MustafaBiyikli/SMAQ/Resources/api.gif

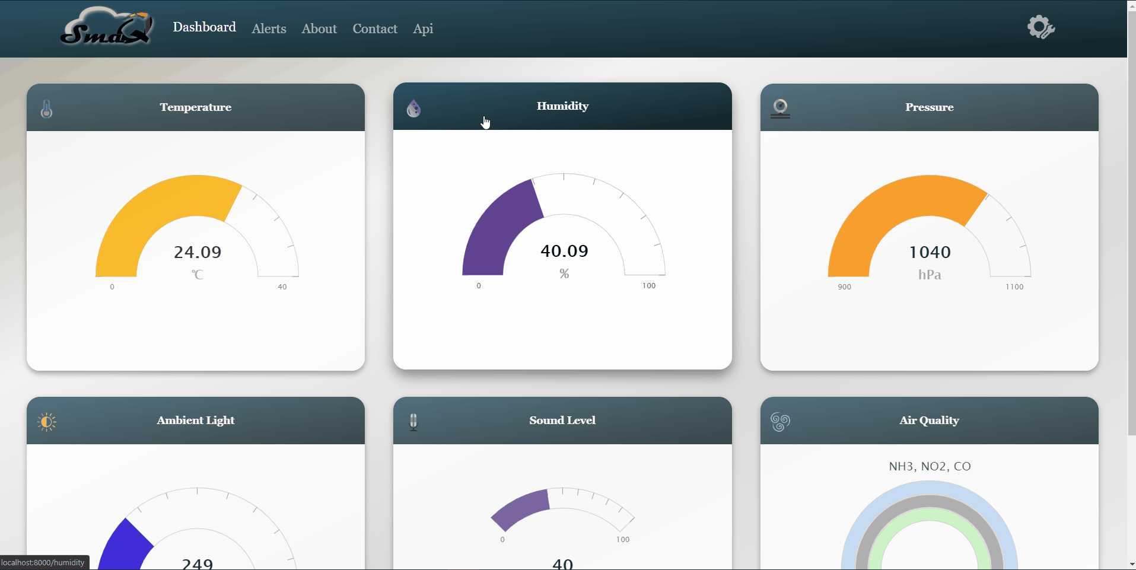
Resources/api.gif
