MustafaBiyikli/SMAQ/Resources/BoxMockupbackside.png

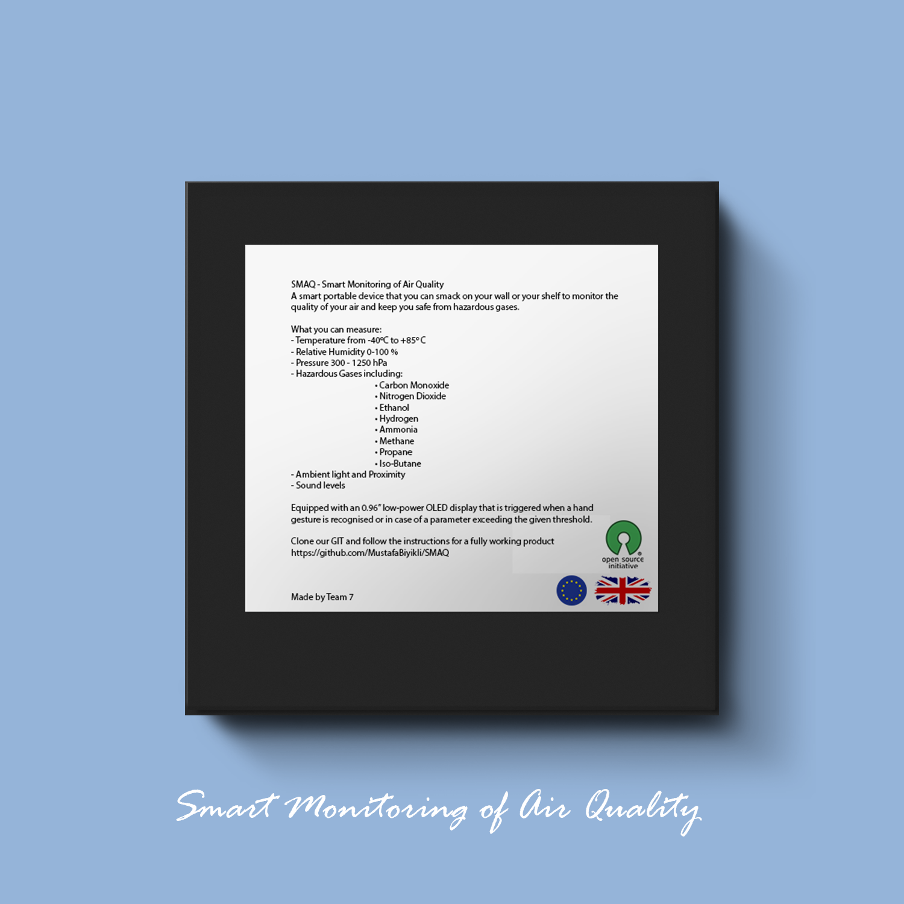
Resources/BoxMockupbackside.png
