MustafaBiyikli/SMAQ/Resources/BoxMockupSide.png

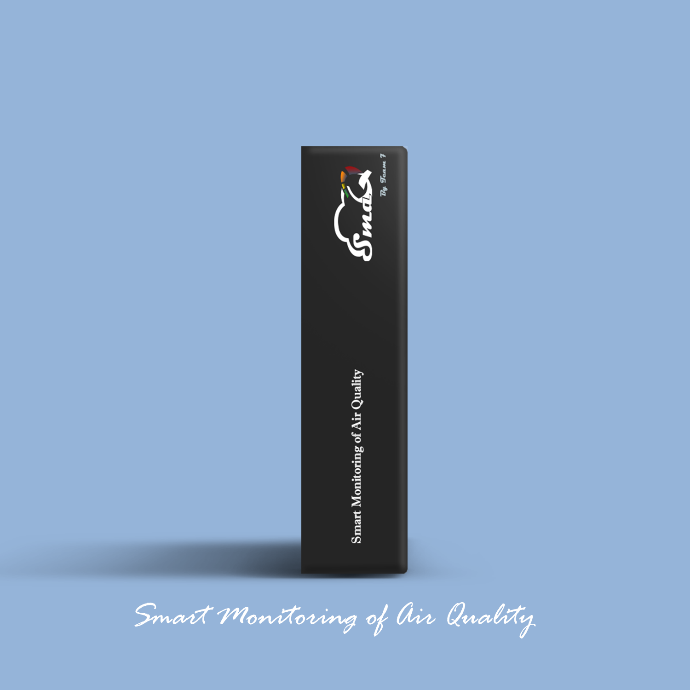
Resources/BoxMockupSide.png
