MustafaBiyikli/SMAQ/Resources/WithBlueBackground.png

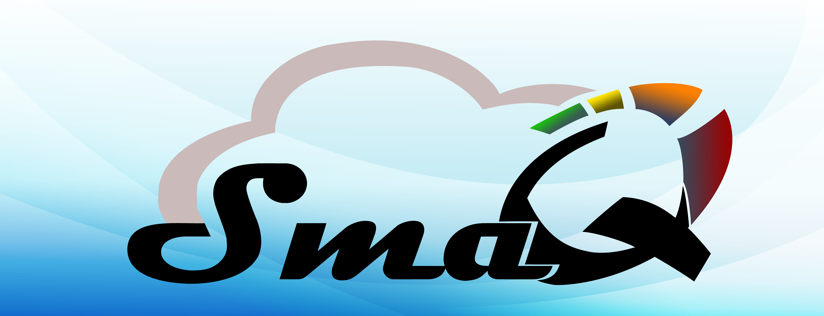
Resources/WithBlueBackground.png
