MustafaBiyikli/SMAQ/Software/Website/img/bgcoral2.jpg

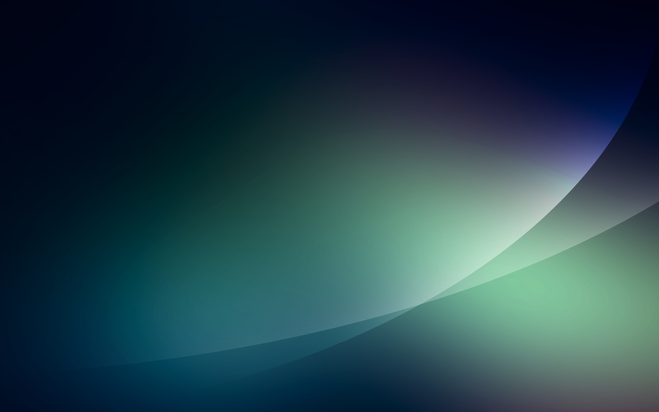
Software/Website/img/bgcoral2.jpg
