MustafaBiyikli/SMAQ/Software/Website/img/colors.jpg

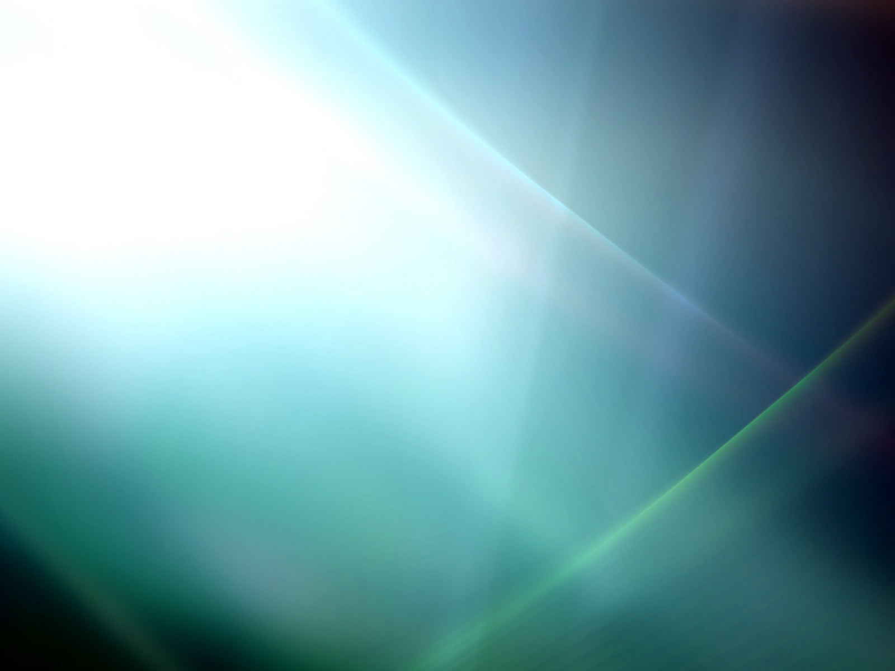
Software/Website/img/colors.jpg
