MustafaBiyikli/SMAQ/Software/Website/img/error.png

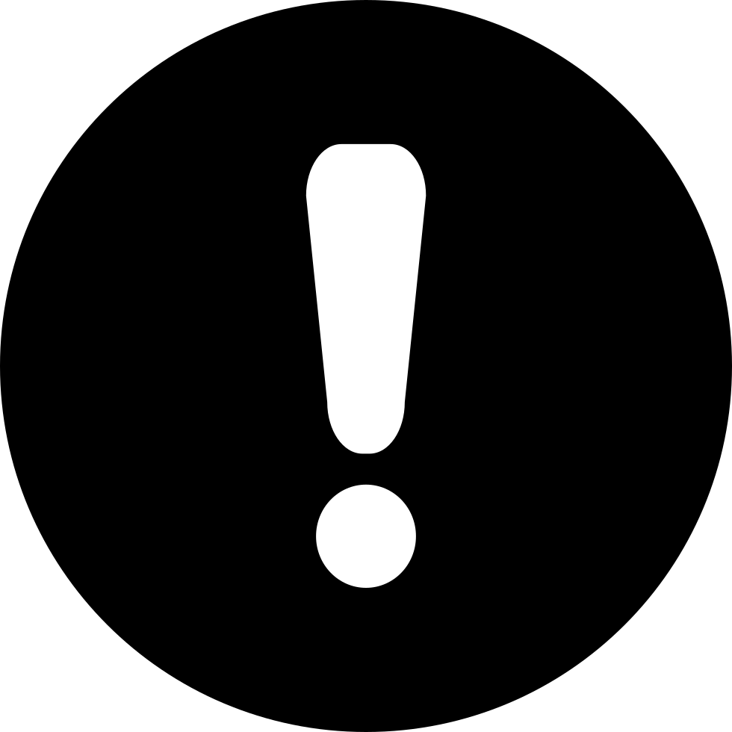
Software/Website/img/error.png
