MustafaBiyikli/SMAQ/Software/Website/img/next.png

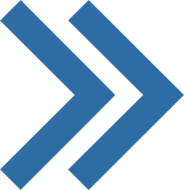
Software/Website/img/next.png
