MustafaBiyikli/SMAQ/Software/Website/img/prev.png

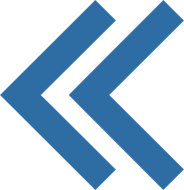
Software/Website/img/prev.png
