MustafaBiyikli/SMAQ/Software/Website/img/settings.png

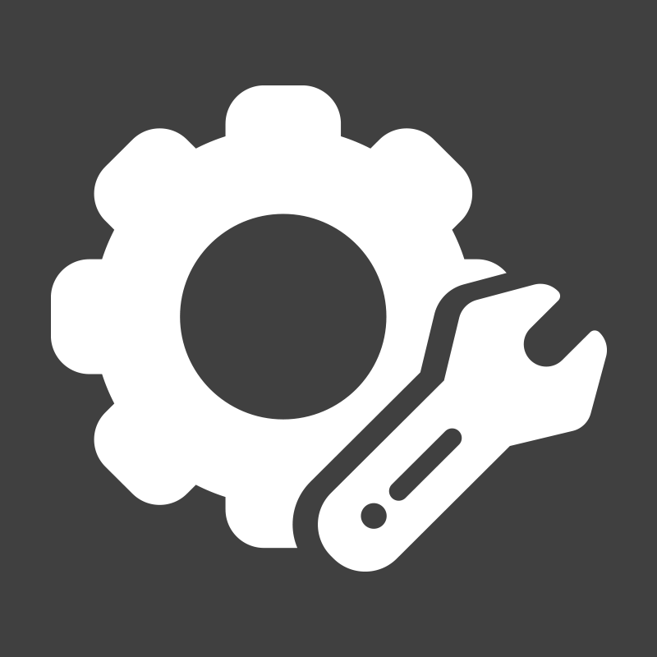
Software/Website/img/settings.png
