MustafaBiyikli/SMAQ/Software/Website/img/success.png

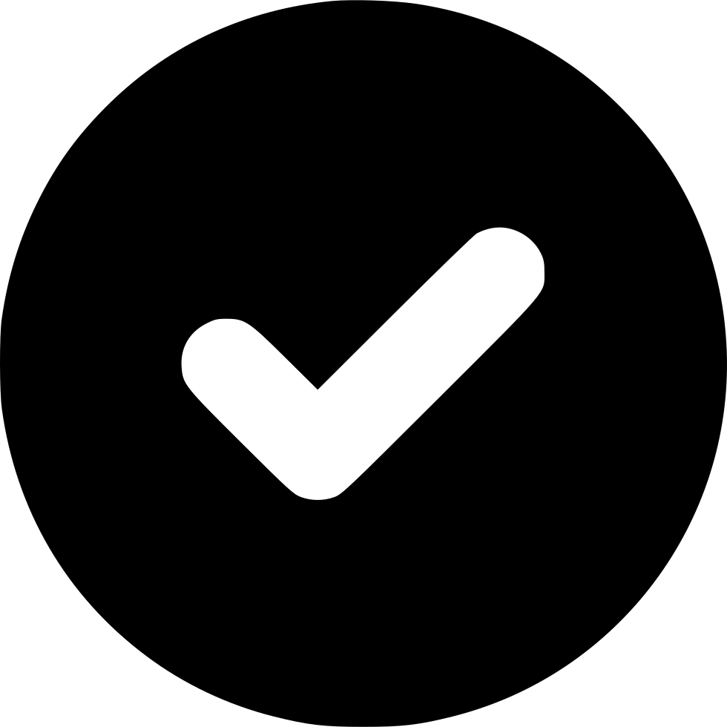
Software/Website/img/success.png
