MustafaBiyikli/SMAQ/Software/Website/img/WebBG.jpg

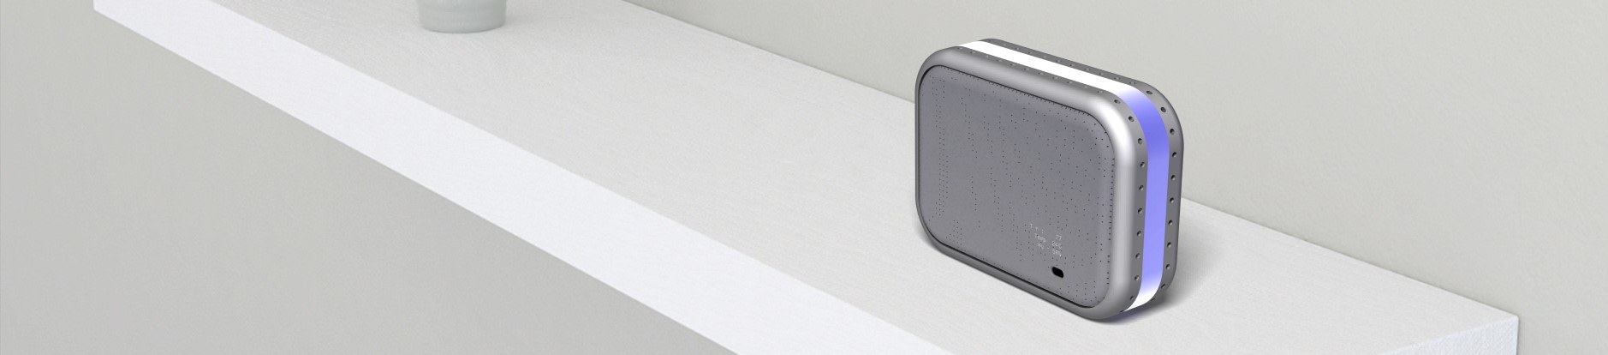
Software/Website/img/WebBG.jpg
