MustafaBiyikli/SMAQ/Hardware/PCB Manufacturing/LayerStackInfo.pdf

# Board Stack Report

Stack Up | Layer Stack
Layer | Board Layer Stack | Name | Material | Thickness | Constant

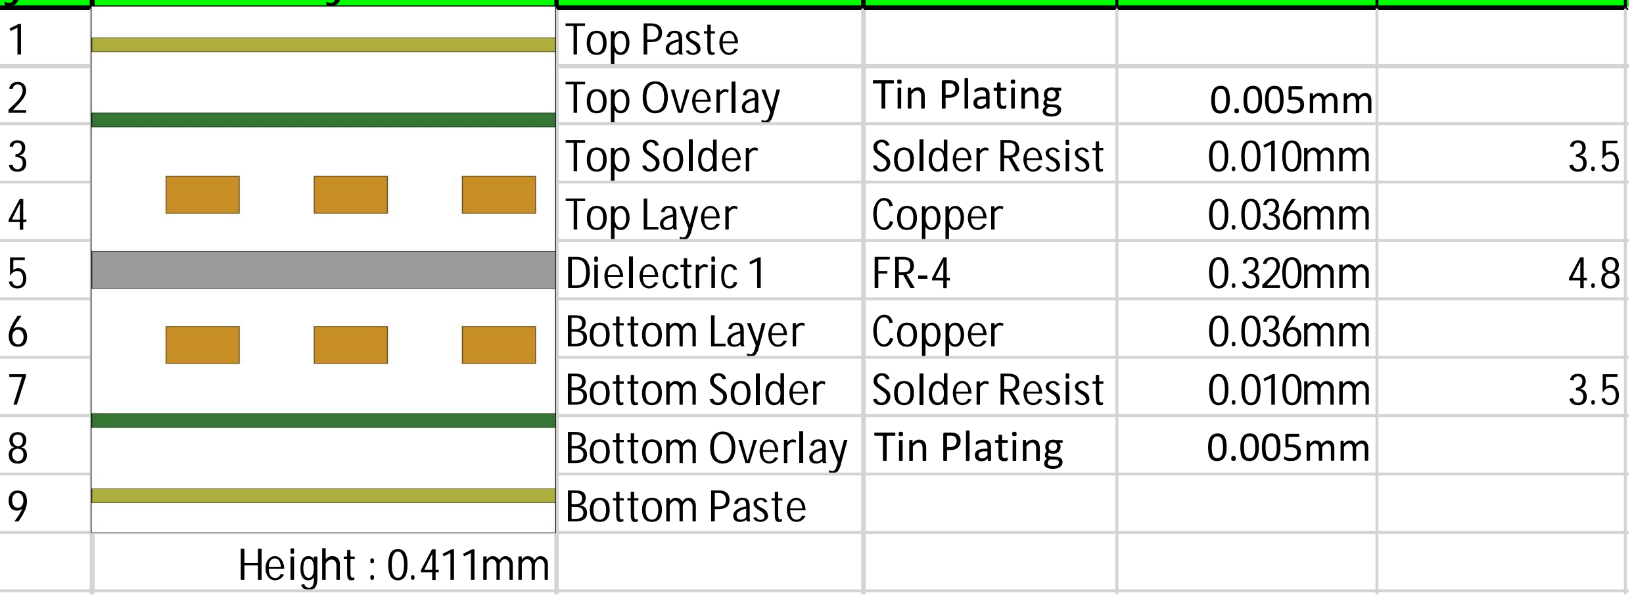
[picture p68: figure]
Top Paste; Top Overlay; Tin Plating; Top Solder; Solder Resist; Top Layer; Copper; Dielectric 1; Bottom Layer; Bottom Solder; Bottom Overlay; Bottom Paste; Height : 0.411mm
