MustafaBiyikli/SMAQ/Hardware/PCB Manufacturing/NC Drill Output/NCDrillOutput.PDF

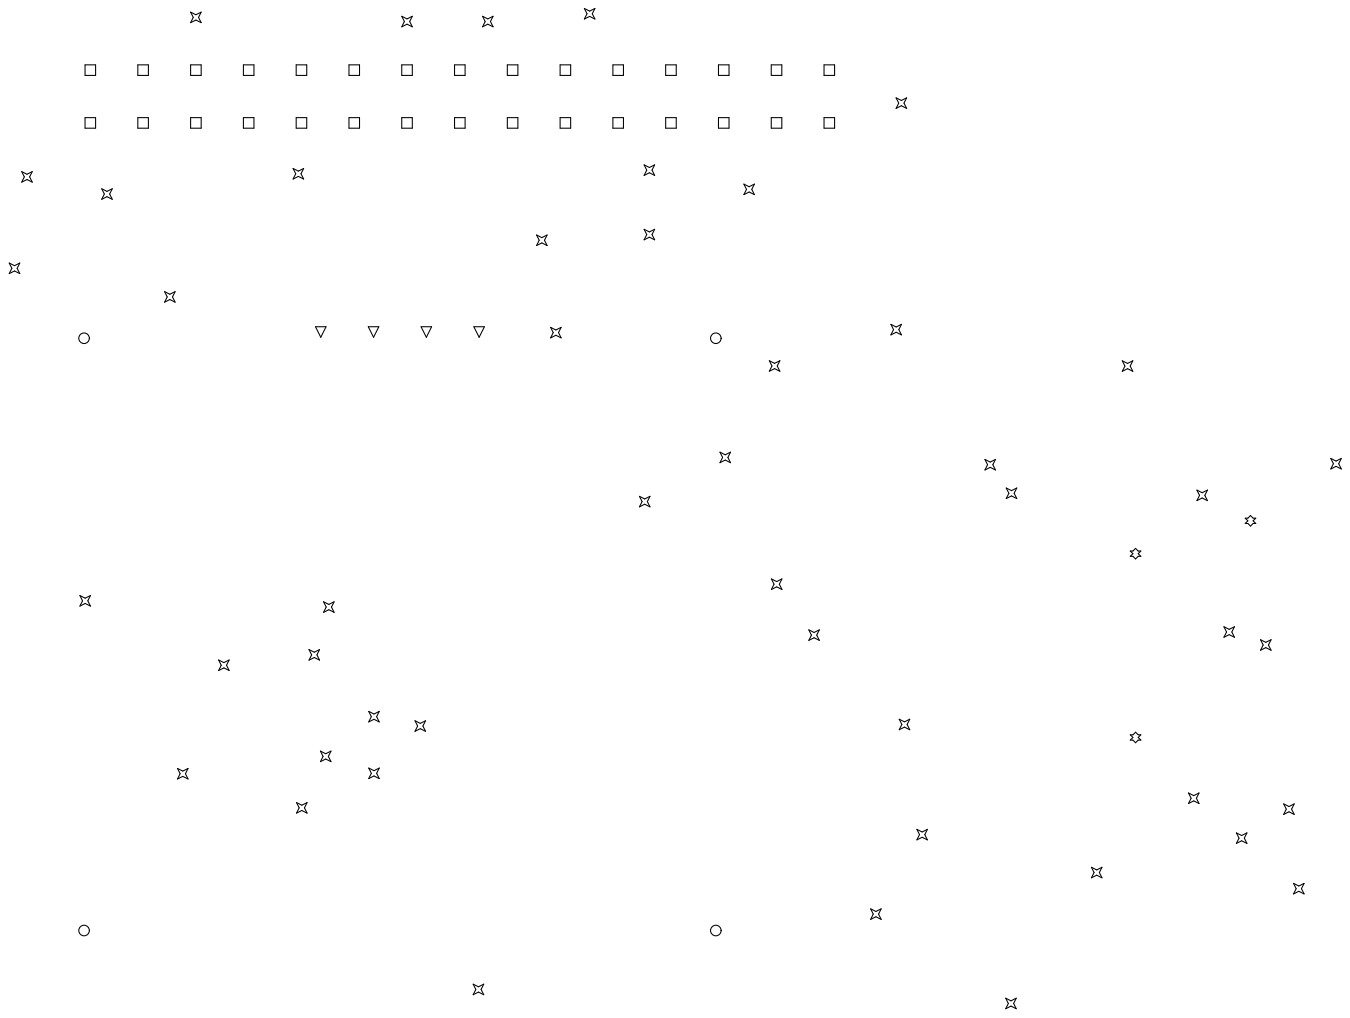
[picture p91: page 1]

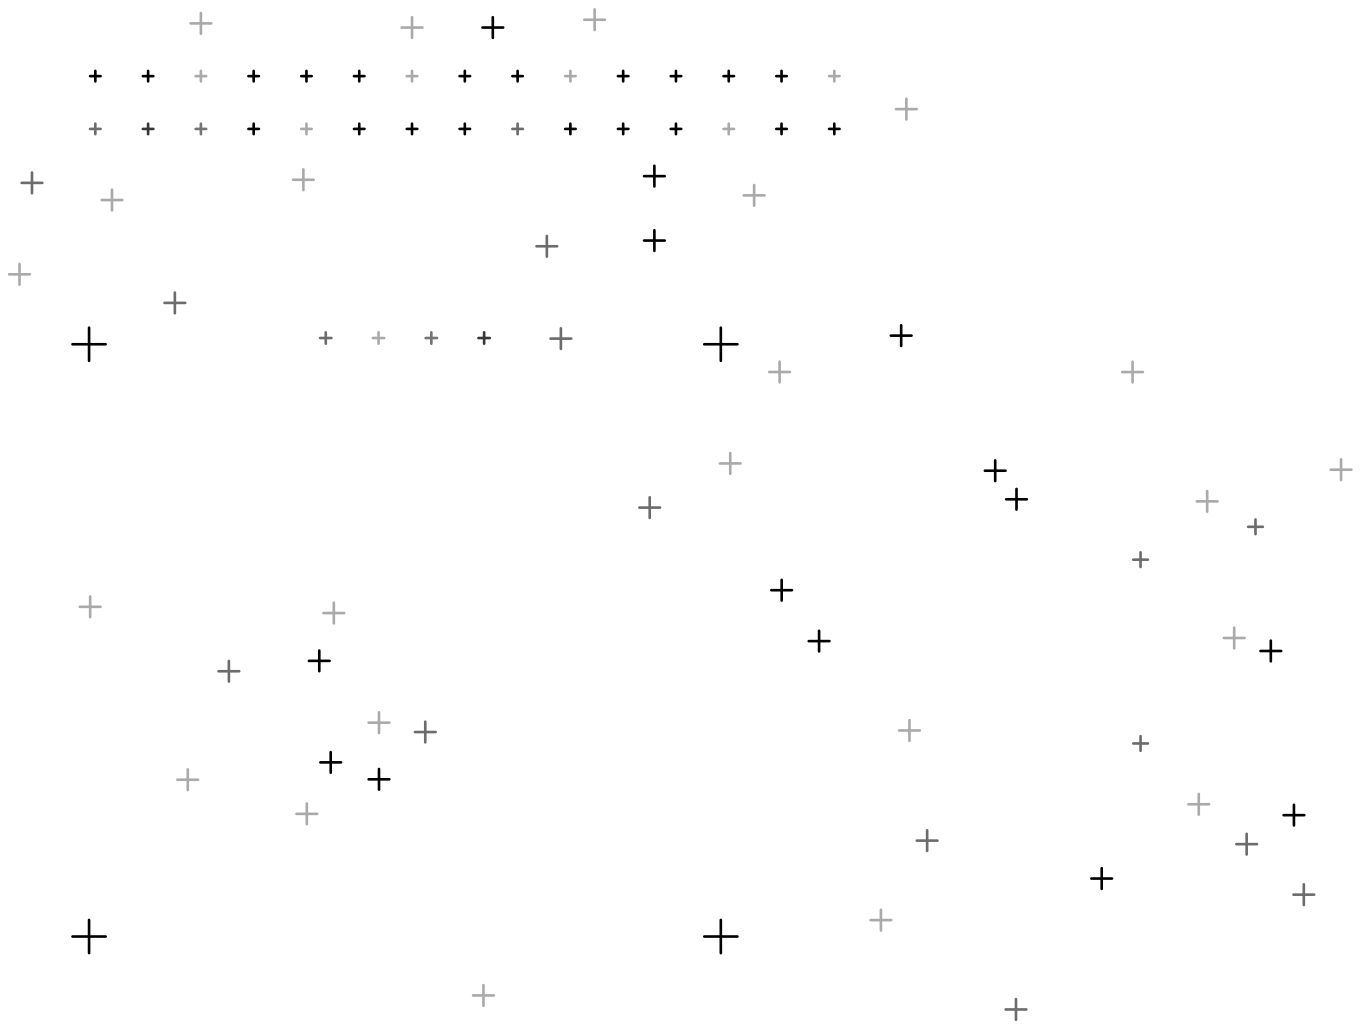
[picture p92: page 2]
