MustafaBiyikli/SMAQ/Hardware/HW_Resources/UofG-Board-etching-SMAQ.pdf

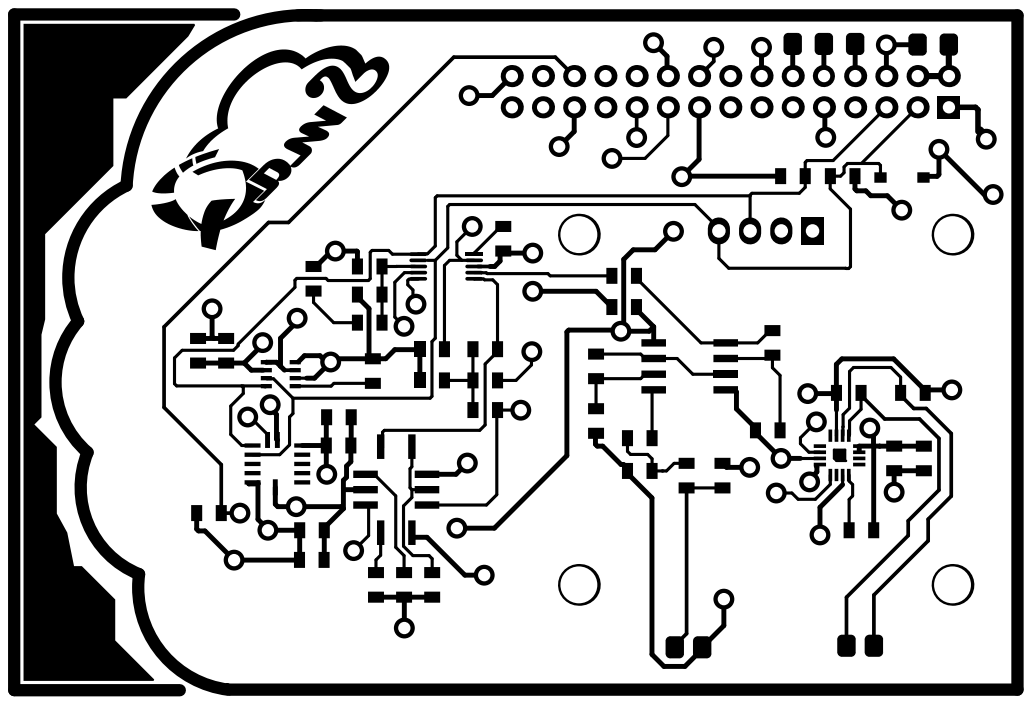
[picture p93: page 1]

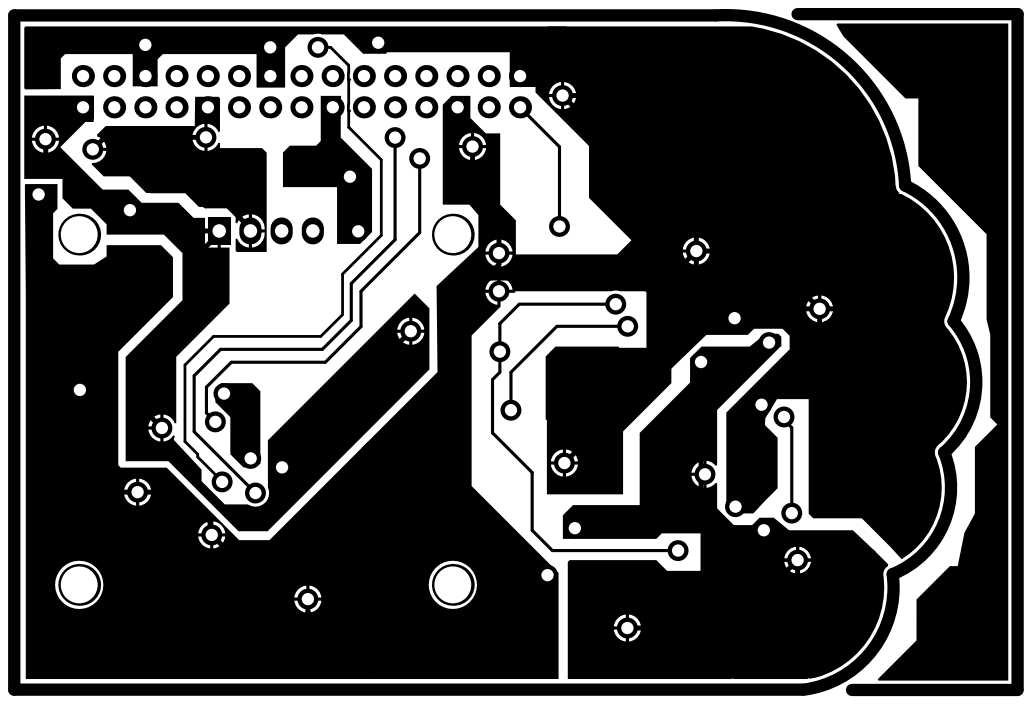
[picture p94: page 2]
