MustafaBiyikli/SMAQ/Software/Real-Time/SH1106.h

#ifndef __SH1106_H__
#define __SH1106_H__

#include <string>
#include <iostream>
using namespace std;

#define rotation 0
#define BLACK 0
#define WHITE 1
#define INVERSE 2

#define SH1106_ADDRESS 0x3C // 011110+SA0+RW - 0x3C or 0x3D

// We use the 128x64 version of SH1106
#define WIDTH 128
#define HEIGHT 64

#define control 0x80

#define SH1106_SETCONTRAST 0x81
#define SH1106_DISPLAYALLON_RESUME 0xA4
#define SH1106_DISPLAYALLON 0xA5
#define SH1106_NORMALDISPLAY 0xA6
#define SH1106_INVERTDISPLAY 0xA7
#define SH1106_DISPLAYOFF 0xAE
#define SH1106_DISPLAYON 0xAF

#define SH1106_SETDISPLAYOFFSET 0xD3
#define SH1106_SETCOMPINS 0xDA

#define SH1106_SETVCOMDETECT 0xDB

#define SH1106_SETDISPLAYCLOCKDIV 0xD5
#define SH1106_SETPRECHARGE 0xD9

#define SH1106_SETMULTIPLEX 0xA8

#define SH1106_SETLOWCOLUMN 0x00  // from 0x00 to 0x0F
#define SH1106_SETHIGHCOLUMN 0x10 // from 0x10 to 0x1F

#define SH1106_SETSTARTLINE 0x40 // from 0x40 to 0x7f

#define SH1106_COLUMNADDR 0x21 // from 0x00 to 0x83
#define SH1106_PAGEADDR 0x22

#define SH1106_COMSCANINC 0xC0
#define SH1106_COMSCANDEC 0xC8

#define SH1106_SEGREMAP 0xA1 // 0xA0 to 0xA1

#define SH1106_CHARGEPUMP 0x8D

#define SH1106_MEMORYMODE 0x20

#define SH1106_EXTERNALVCC 0x1
#define SH1106_SWITCHCAPVCC 0x2

class SH1106
{
public:
    /** Declare Functions */
    void sh1106_init(int fd_SH1106);
    void sh1106_display(int fd_SH1106);
    void sh1106_clearDisplay(int fd_SH1106);
    void sh1106_displayOFF(int fd_SH1106);
    void sh1106_drawPixel(int x, int y, unsigned int color);
    void sh1106_write(int c);
    void sh1106_drawString(string str);
    void sh1106_drawChar(int x, int y, unsigned char c, int color, int size = 1);
    string getDateTime(int date_or_time);
    void sh1106_displayData(int fd_SH1106, int t, int p, int h, int lux);

    // Used for date_or_time in getDateTime fn
    int DATE = 0;
    int TIME = 1;

    /** SMAQ logo bmp buffer */
    int buffer[WIDTH * HEIGHT / 8] =
        {
            0x00, 0x00, 0x00, 0x00, 0x00, 0x00, 0x00, 0x00, 0x00, 0x00, 0x00, 0x00, 0x00, 0x00, 0x00, 0x00,
            0x00, 0x00, 0x00, 0x00, 0x00, 0x00, 0x00, 0x00, 0x00, 0x00, 0x00, 0x00, 0x00, 0x00, 0x00, 0x00,
            0x00, 0x00, 0x00, 0x00, 0x00, 0x00, 0x00, 0x00, 0x00, 0x00, 0x00, 0x00, 0x00, 0x00, 0x00, 0x00,
            0x00, 0x00, 0x00, 0x00, 0x00, 0x00, 0x00, 0x00, 0x00, 0x00, 0x00, 0x00, 0x00, 0x00, 0x00, 0x00,
            0x00, 0x00, 0x00, 0x00, 0x00, 0x00, 0x00, 0x00, 0x00, 0x00, 0x00, 0x00, 0x00, 0x00, 0x00, 0x00,
            0x00, 0x00, 0x00, 0x00, 0x00, 0x00, 0x00, 0x00, 0x00, 0x00, 0x00, 0x00, 0x00, 0x00, 0x00, 0x00,
            0x00, 0x00, 0x00, 0x00, 0x00, 0x00, 0x00, 0x00, 0x00, 0x00, 0x00, 0x00, 0x00, 0x00, 0x00, 0x00,
            0x00, 0x00, 0x00, 0x00, 0x00, 0x00, 0x00, 0x00, 0x00, 0x00, 0x00, 0x00, 0x00, 0x00, 0x00, 0x00,

            0x00, 0x00, 0x00, 0x00, 0x00, 0x00, 0x00, 0x00, 0x00, 0x00, 0x00, 0x00, 0x00, 0x00, 0x00, 0x00,
            0x00, 0x00, 0x00, 0x00, 0x00, 0x00, 0x00, 0x00, 0x00, 0x00, 0x00, 0x00, 0x00, 0x00, 0x00, 0x00,
            0x00, 0x00, 0x80, 0xC0, 0xE0, 0xF0, 0x70, 0x78, 0x3C, 0x3C, 0x1C, 0x0C, 0x0E, 0x0E, 0x06, 0x06,
            0x06, 0x06, 0x06, 0x06, 0x07, 0x03, 0x03, 0x02, 0x02, 0x02, 0x06, 0x06, 0x06, 0x06, 0x06, 0x06,
            0x04, 0x0C, 0x0C, 0x1C, 0x18, 0x38, 0x30, 0x60, 0xE0, 0xC0, 0x80, 0x00, 0x00, 0x00, 0x00, 0x00,
            0x00, 0x00, 0x00, 0x00, 0x00, 0x00, 0x00, 0x00, 0x00, 0x00, 0x00, 0x00, 0x00, 0x00, 0x00, 0x00,
            0x00, 0x00, 0x00, 0x00, 0x00, 0x00, 0x00, 0x00, 0x00, 0x00, 0x00, 0x00, 0x00, 0x00, 0x00, 0x00,
            0x00, 0x00, 0x00, 0x00, 0x00, 0x00, 0x00, 0x00, 0x00, 0x00, 0x00, 0x00, 0x00, 0x00, 0x00, 0x00,

            0x00, 0x00, 0x00, 0x00, 0x00, 0x00, 0x00, 0x00, 0x00, 0x00, 0x00, 0x00, 0x00, 0x00, 0x00, 0x00,
            0x00, 0x00, 0x00, 0x00, 0x00, 0x00, 0x00, 0x00, 0x00, 0x00, 0x00, 0x00, 0x00, 0x00, 0x80, 0x80,
            0xFC, 0xFE, 0x0F, 0x03, 0x01, 0x00, 0x00, 0x00, 0x00, 0x00, 0x00, 0x00, 0x00, 0x00, 0x00, 0x00,
            0x00, 0x00, 0x00, 0x00, 0x00, 0x00, 0x00, 0x00, 0x00, 0x00, 0x00, 0x00, 0x00, 0x00, 0x00, 0x00,
            0x00, 0x00, 0x00, 0x00, 0x00, 0x00, 0x00, 0x00, 0x00, 0x01, 0x03, 0x07, 0x04, 0x00, 0x00, 0x00,
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
            0x03, 0x03, 0x01, 0x01, 0x01, 0x01, 0x00, 0x00, 0x00, 0x00, 0x00, 0x00, 0x00, 0x00, 0x00, 0x01,
            0x01, 0x01, 0x03, 0x01, 0x00, 0x00, 0x00, 0x00, 0x00, 0x00, 0x00, 0x00, 0x00, 0x00, 0x00, 0x00,

            0x00, 0x00, 0x00, 0x00, 0x00, 0x00, 0x00, 0x00, 0x00, 0x00, 0x00, 0x00, 0x00, 0x00, 0x00, 0x00,
            0x00, 0x00, 0x00, 0x00, 0x00, 0x00, 0x00, 0x00, 0x00, 0x00, 0x00, 0x00, 0x00, 0x00, 0x00, 0x00,
            0x00, 0x00, 0x00, 0x00, 0x00, 0x00, 0x00, 0x00, 0x00, 0x00, 0x00, 0x00, 0x00, 0x00, 0x00, 0x00,
            0x00, 0x00, 0x00, 0x00, 0x00, 0x00, 0x00, 0x00, 0x00, 0x00, 0x00, 0x00, 0x00, 0x00, 0x00, 0x00,
            0x00, 0x00, 0x00, 0x00, 0x00, 0x00, 0x00, 0x00, 0x00, 0x00, 0x00, 0x00, 0x00, 0x00, 0x00, 0x00,
            0x00, 0x00, 0x00, 0x00, 0x00, 0x00, 0x00, 0x00, 0x00, 0x00, 0x00, 0x00, 0x00, 0x00, 0x00, 0x00,
            0x00, 0x00, 0x00, 0x00, 0x00, 0x00, 0x00, 0x00, 0x00, 0x00, 0x00, 0x00, 0x00, 0x00, 0x00, 0x00,
            0x00, 0x00, 0x00, 0x00, 0x00, 0x00, 0x00, 0x00, 0x00, 0x00, 0x00, 0x00, 0x00, 0x00, 0x00, 0x00};
};

#endif
