MustafaBiyikli/SMAQ/Software/Website/example-config.env.txt

EMAIL_USERNAME=<mailtrap_smtp_username>
EMAIL_PASSWORD=<mailtrap_smtp_password>
EMAIL_HOST=smtp.mailtrap.io
EMAIL_PORT=25
EMAIL_FROM=<your_email_address>

SENDGRID_USERNAME=apikey
SENDGRID_PASSWORD=<sendgrid_password>
